hawkowl/split-flap/src/main.hpp

void receiveLetter(int numBytes);
void requestEvent();
int getaddress();
void getOffset();
int calibrate(bool initialCalibration);
void stopMotor();
void startMotor();
void rotateToLetter(int toLetter);
